openMLA/photon-ultra-controller-rp2040/src/test_image.c

// not a very elegant way of storing this information. 

// paste big comma separated hex list below. You can use the utils/grayscale_tiff_to_bytes.py to
// generate this
unsigned char DLP_data_array[230400];  // = {};
